bardolf/meshcore-repeater/media/11_neighbors.jpg

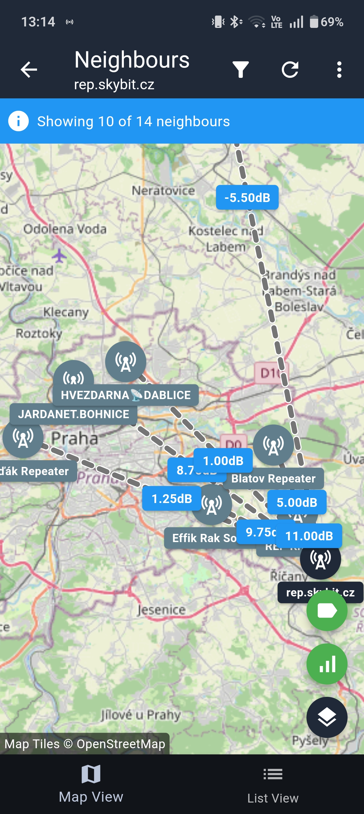
media/11_neighbors.jpg
